alecjprobst/SlimeVRMotherboard/Images/IMU_ROTATIONixed.png

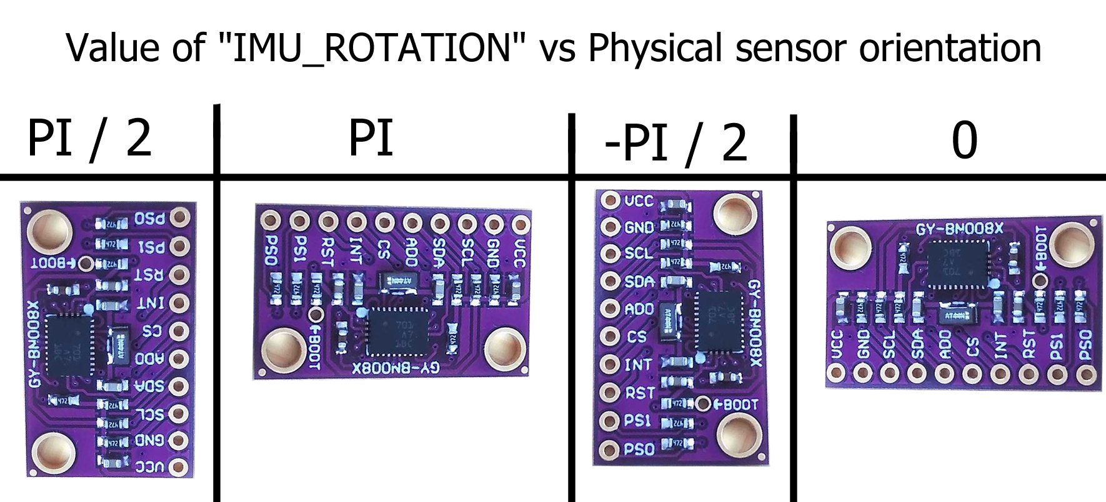
Images/IMU_ROTATIONixed.png
