alecjprobst/SlimeVRMotherboard/KiCAD Schematic/SlimeVRMotherBoard/wemos-d1-mini-kicad-master/meta/illustration1.png

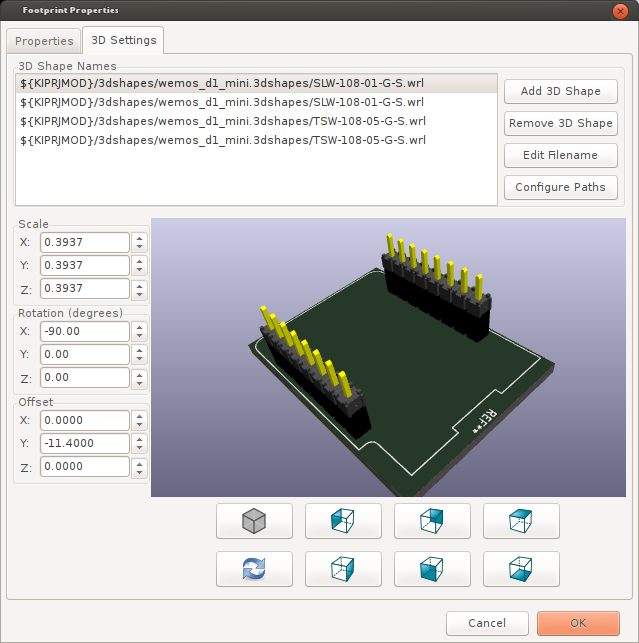
KiCAD Schematic/SlimeVRMotherBoard/wemos-d1-mini-kicad-master/meta/illustration1.png
