alecjprobst/SlimeVRMotherboard/KiCAD Schematic/SlimeVRMotherBoard/wemos-d1-mini-kicad-master/meta/illustration2.png

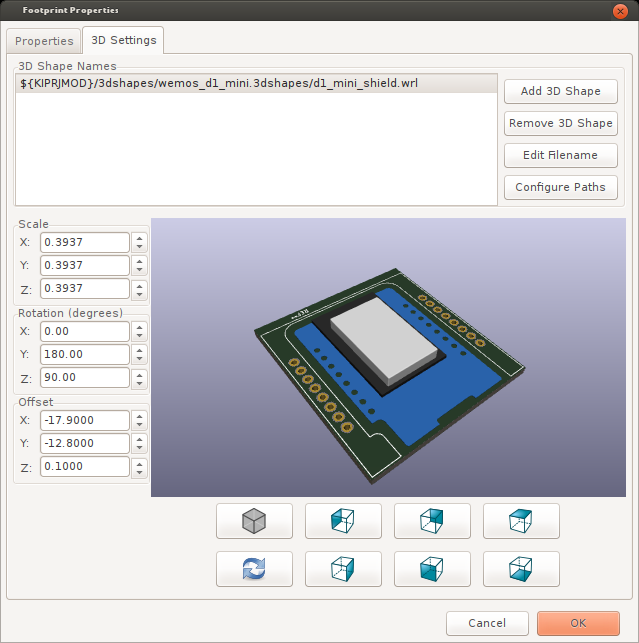
KiCAD Schematic/SlimeVRMotherBoard/wemos-d1-mini-kicad-master/meta/illustration2.png
